giampierobartolomei/Echo/firmware/model_alldata.h

#pragma once
#include <cstdarg>
namespace Eloquent {
    namespace ML {
        namespace Port {
            class DecisionTree {
                public:
                    /**
                    * Modello addestrato usando dati da tutti i soggetti + embedded test (classe2=frog)
                    */
                    int predict(float *x) {
                        if (x[17] <= 4.360803127288818) {
                            if (x[0] <= 0.7058824896812439) {
                                if (x[8] <= 9.176472187042236) {
                                    if (x[18] <= 3.921568512916565) {
                                        if (x[15] <= 0.275421679019928) {
                                            if (x[18] <= 1.5007190704345703) {
                                                return 3;
                                            }

                                            else {
                                                return 3;
                                            }
                                        }

                                        else {
                                            return 3;
                                        }
                                    }

                                    else {
                                        if (x[19] <= 4.139490962028503) {
                                            return 3;
                                        }

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
                                            }

                                            else {
                                                if (x[18] <= 221.33538055419922) {
                                                    return 0;
                                                }
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
